EiNSTeiN-/roadrunner-filament-sensor/images/manual/001_parts.jpg

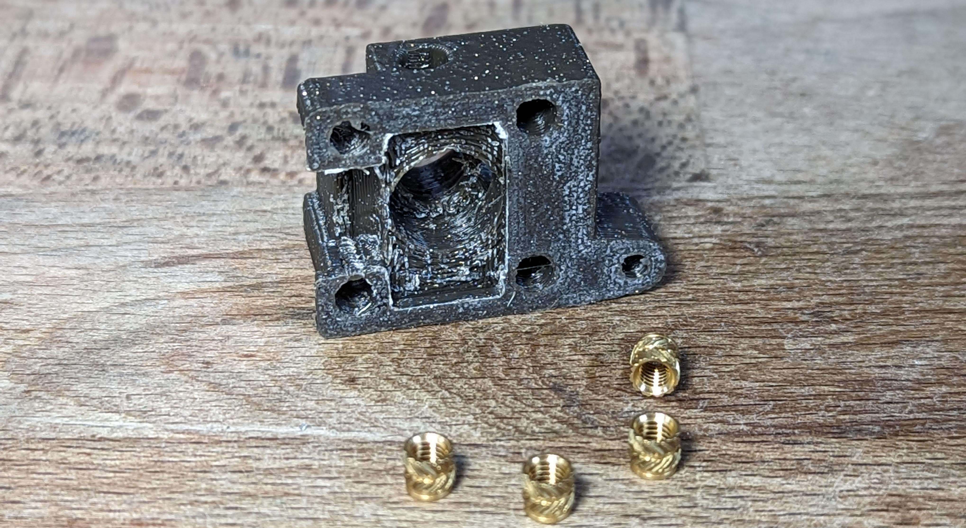
images/manual/001_parts.jpg
