EiNSTeiN-/roadrunner-filament-sensor/images/manual/002_parts.jpg

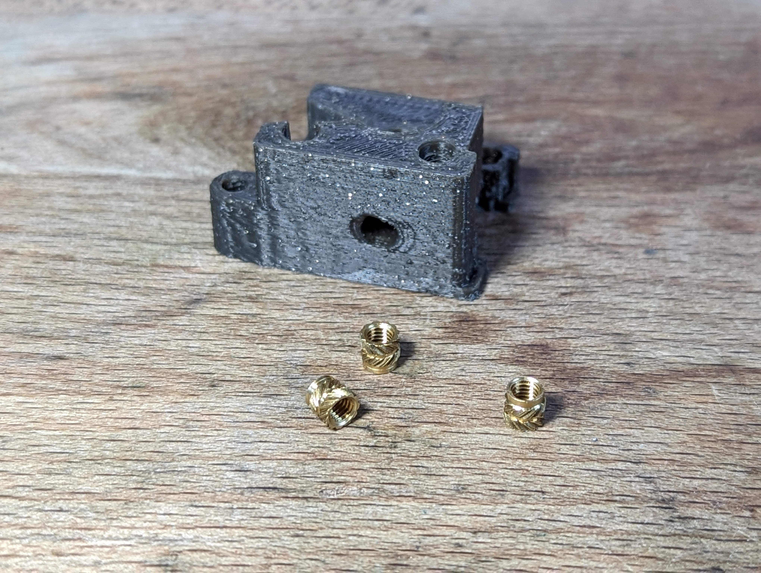
images/manual/002_parts.jpg
