EiNSTeiN-/roadrunner-filament-sensor/images/manual/012_assembled.jpg

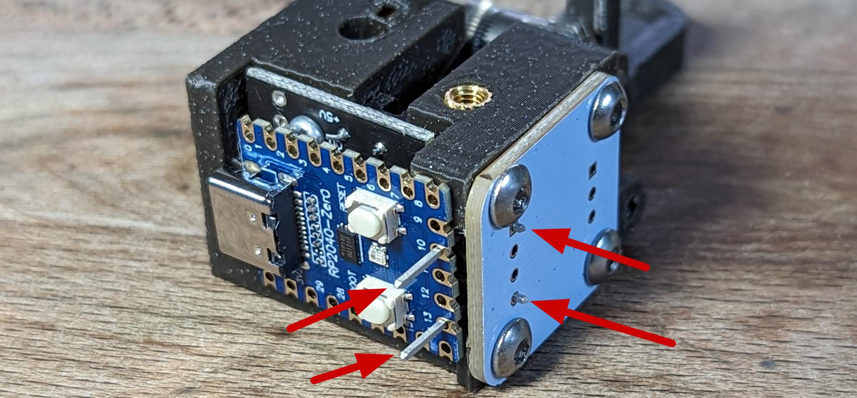
images/manual/012_assembled.jpg
