EiNSTeiN-/roadrunner-filament-sensor/images/manual/012_soldered_1.jpg

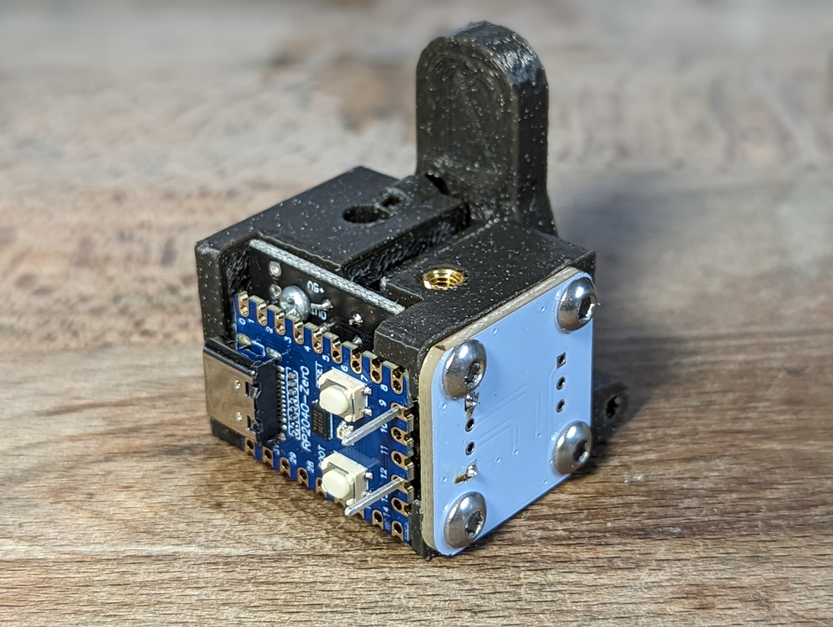
images/manual/012_soldered_1.jpg
