EiNSTeiN-/roadrunner-filament-sensor/images/manual/013_soldered_1.jpg

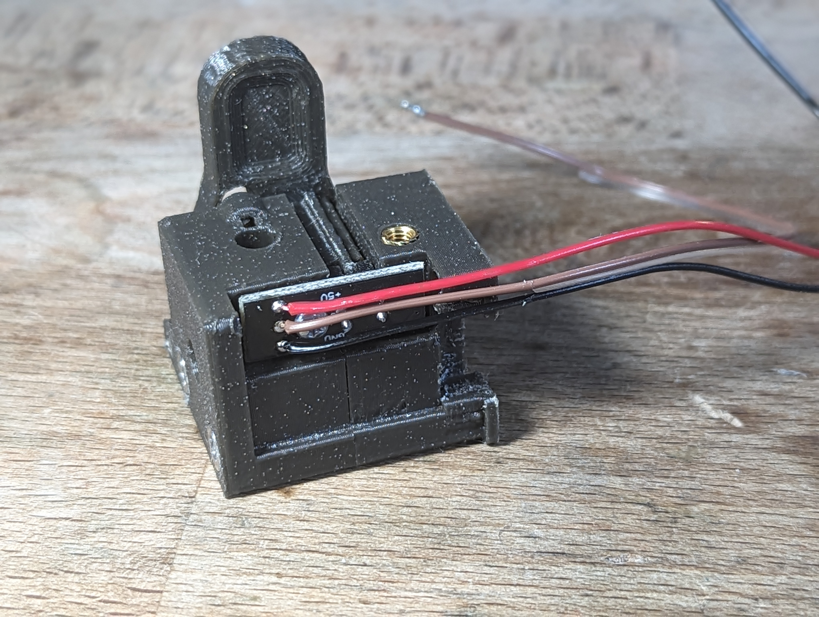
images/manual/013_soldered_1.jpg
