EiNSTeiN-/roadrunner-filament-sensor/images/manual/014_soldered_1.jpg

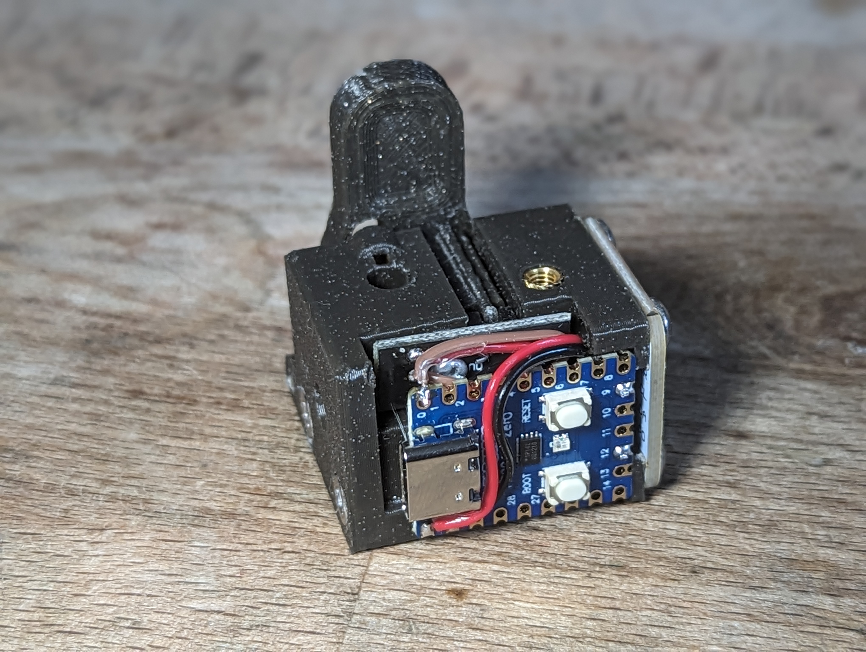
images/manual/014_soldered_1.jpg
