EiNSTeiN-/roadrunner-filament-sensor/images/manual/019_filament_inserted.png

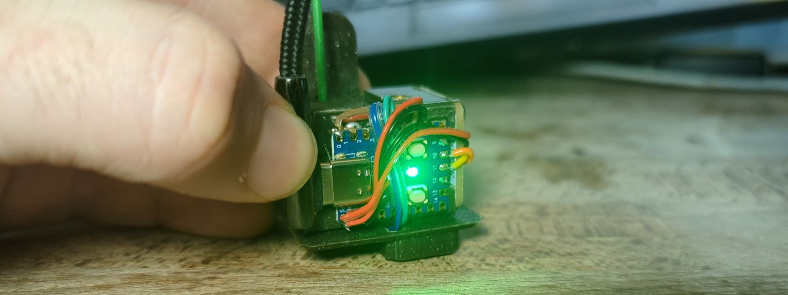
images/manual/019_filament_inserted.png
