EiNSTeiN-/roadrunner-filament-sensor/images/manual/019_no_filament.png

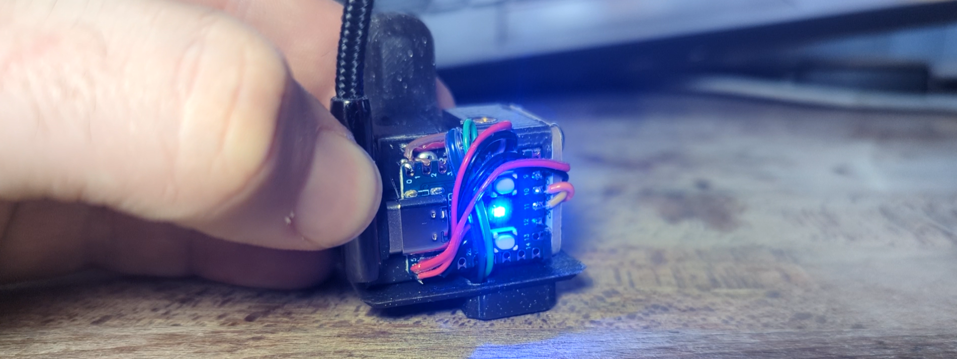
images/manual/019_no_filament.png
