EiNSTeiN-/roadrunner-filament-sensor/images/manual/020_assembled_2.jpg

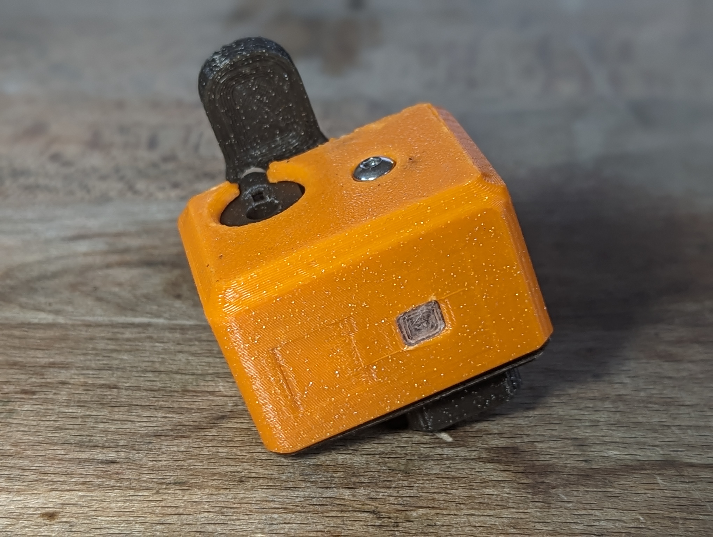
images/manual/020_assembled_2.jpg
