EiNSTeiN-/roadrunner-filament-sensor/klippy/extras/high_resolution_filament_sensor.py

# High Resolution Filament Sensor
#
# Copyright (C) 2023 Francois Chagnon <fc@francoischagnon.net>
#
# This file may be distributed under the terms of the GNU GPLv3 license.
import struct
import logging
import typing
import serialhdl
import serial
from . import bus, filament_switch_sensor, tmc_uart, high_resolution_filament_sensor_calibration as calibration

DEFAULT_I2C_TARGET_ADDR = 0x40
DEFAULT_I2C_SPEED = 100000

CHECK_RUNOUT_TIMEOUT = .100 # read sensor value at this interval

VIRTUAL_MOTION_PREFIX = 'virtual_motion_sensor'
VIRTUAL_SWITCH_PREFIX = 'virtual_switch_sensor'

class MagnetState:
    """" State of the rotary magnet encoder inside the sensor. """
    NOT_DETECTED = 1
    TOO_WEAK = 2
    TOO_STRONG = 3
    DETECTED = 4

    VALUES : dict[int, str] = {
        NOT_DETECTED: "not detected",
        TOO_WEAK: "too weak",
        TOO_STRONG: "too strong",
        DETECTED: "detected",
    }

    def __init__(self, value : int):
        self.value = value

    def __str__(self):
        return MagnetState.VALUES.get(self.value, "unknown")

    def __repr__(self):
        return "%s(value=%s)" % (self.__class__.__name__, repr(self.value))

class SensorRegister:
    """ Enum of registers that can be read from the sensor. """
    ALL = 0x10
    MAGNET_STATE = 0x21
    FILAMENT_PRESENCE = 0x22
    FULL_TURNS = 0x23
    ANGLE = 0x24

    def __init__(self, magnet_state, filament_presence, full_turns, angle):
        self.magnet_state = magnet_state
        self.filament_presence = filament_presence
        self.full_turns = full_turns
        self.angle = angle
        self.connected = not (magnet_state is None or
                                filament_presence is None or
                                full_turns is None or
                                angle is None)

class SensorEvent:
    """ A point-in-time reading from the sensor, which holds calculated
    values as well as additional printer state. """

    def __init__(self, eventtime : float, position : float, distance : float, epos : float):
        # eventtime at which this sensor reading was taken
        self.eventtime = eventtime

        # sensor position
        self.position = position

        # distance since previous reading from the sensor
        self.distance = distance

        # estimated extruder position at this eventtime
        self.epos = epos

    def __repr__(self):
        return "%s(eventtime=%s, position=%s, distance=%s, epos=%s)" % (
            self.__class__.__name__, self.eventtime, self.position, self.distance, self.epos)

class SensorUART(tmc_uart.MCU_TMC_uart_bitbang):
    """ Class for reading from the sensor via Klipper's native TMC uart driver. """

    def _remove_serial_bits(self, data : str) -> bytearray:
        """ Remove serial start and stop bits to a message in a bytearray. """
        mval = pos = 0
        for d in bytearray(data):
            mval |= d << pos
            pos += 8

        pos = 0
        res = bytearray()
        for i in range((len(data) * 8) // 10):
           shift = (i * 10) + 1
           res.append((mval >> shift) & 0xff)
        return res

    def _decode_read(self, reg : int, data : str) -> typing.Optional[bytearray]:
        """ Extract a uart read response message and returns the decoded message.
        Returns None when message cannot be verified. """
        decoded = self._remove_serial_bits(data)
        if len(decoded) < 5:
            return None
        if decoded[-1] != self._calc_crc8(decoded[:-1]):
            return None
        if decoded[0] != 0x05 and decoded[1] != 0xff:
            logging.warning("Received wrong message prefix: %s" % (decoded.hex(), ))
            return None
        if decoded[2] != reg:
            logging.warning("Received response for reg %02x (expected %02x)" % (decoded[2], reg))
            return None
        return decoded[3:-1]

    def reg_read(self, _instance_id, addr : int, reg : int, reg_length : int = 4) -> typing.Optional[bytearray]:
        """ Read a single register and returns a bytearray. """
        msg = self._encode_read(0xf5, addr, reg)
        read_length = (((4 + reg_length) * 10) + 7) // 8
        params = self.tmcuart_send_cmd.send([self.oid, msg, read_length])
        return self._decode_read(reg, params['read'])

class RegisterReaderGeneric:
    def __init__(self): pass
    def read(self) -> SensorRegister: raise NotImplementedError('must be implemented in subclass')

class RegisterReaderUART(RegisterReaderGeneric):
    def __init__(self, uart):
        self.uart = uart

    def read(self):
        magnet_state = self.uart_read_reg1(SensorRegister.MAGNET_STATE)
        filament_presence = self.uart_read_reg1(SensorRegister.FILAMENT_PRESENCE)
        full_turns = self.uart_read_reg4(SensorRegister.FULL_TURNS)
        angle = self.uart_read_reg4(SensorRegister.ANGLE)

        return SensorRegister(magnet_state, filament_presence, full_turns, angle)

    def uart_read_reg(self, reg, length, retries=5):
        for _ in range(retries):
            response = self.uart.reg_read(None, 0, reg, length)
            if response:
                break
        if response is None:
            logging.warning("Error reading from uart, no response received or CRC was invalid.")
        else:
            return response

    def uart_read_reg4(self, reg):
        if data := self.uart_read_reg(reg, 4):
            val, = struct.unpack('<l', data)
            return val

    def uart_read_reg1(self, reg):
        if data := self.uart_read_reg(reg, 1):
            val, = struct.unpack('<B', data)
            return val

class RegisterReaderI2C(RegisterReaderGeneric):
    def __init__(self, i2c):
        self.i2c = i2c
        self.printer = i2c.mcu.get_printer()

    def read(self):
        data = self.i2c_read_reg(SensorRegister.ALL, 10)
        if not data or len(data) != 10:
            if data:
                error = "expected 10 bytes but got %d: '%s'" % (len(data), data.hex(), )
            else:
                error = "communication error"
            logging.warning(f"Reading from sensor failed: {error}")
            return

        magnet_state, filament_presence, full_turns, angle = struct.unpack('<BBll', data)
        if magnet_state == 0xff:
            return

        return SensorRegister(magnet_state, filament_presence, full_turns, angle)

    def i2c_read_reg(self, reg, length):
        try:
            params = self.i2c.i2c_read([reg], length)
            return bytearray(params['response'])
        except (serialhdl.error, self.printer.command_error) as e:
            logging.warning(f"{self.name}: Unable to read: {e}")
            return

class RegisterReaderSerial(RegisterReaderGeneric):
    def __init__(self, serial : serial.Serial):
        self.serial = serial
        self.buffer = bytes()

    def read(self):
        try:
            if self.serial.write(bytearray([0xf5, SensorRegister.ALL])) != 2:
                logging.warning(f"Writing to serial failed")
                return

            while True:
                data = self.serial.read()
                if len(data) == 0:
                    break
                self.buffer += data

            marker = None
            for i in range(len(self.buffer)-1):
                if self.buffer[i] == 0x05 and self.buffer[i+1] == 0xff:
                    marker = i
                    break

            if marker is None:
                logging.warning(f"Failed to find register marker in buffer")
                self.buffer = bytes()
                return

            if len(self.buffer) < 13:
                logging.warning(f"Not enough bytes read for response")
                return

            if (r := self.buffer[marker+2]) != SensorRegister.ALL:
                logging.warning(f"Wrong register response ({r!r})")
                self.buffer = self.buffer[marker+1:]
                return

            data = self.buffer[marker+3:marker+13]
            self.buffer = self.buffer[marker+13:]
        except serial.SerialException:
            logging.error("Unable to communicate with sensor")
            return

        if not data or len(data) != 10:
            if data:
                error = "expected 10 bytes but got %d: '%s'" % (len(data), data.hex(), )
            else:
                error = "communication error"
            logging.warning(f"Reading from sensor failed: {error}")
            return

        magnet_state, filament_presence, full_turns, angle = struct.unpack('<BBll', data)
        if magnet_state == 0xff:
            return

        return SensorRegister(magnet_state, filament_presence, full_turns, angle)

class SensorRotationHelper:
    """ Helper class used to convert raw point-in-time readings from the sensor
    into an angular change since the previous reading. """

    def __init__(self, resolution : int, ignore_bits : int):
        self.resolution = resolution
        self.ignore_bits = ignore_bits

        # Maximum and minimum values that can be obtained from the sensor
        self.angle_max_value = (1 << resolution) - 1
        self.angle_min_value = (1 << ignore_bits)

        # Value used to mask lower bits of the raw angle value read from the printer.
        self.mask = (1 << ignore_bits) - 1

        # The cumulative angle value including all full turns,
        # kept in the sensor's original resolution.
        self._absolute_angular_position = 0

    @property
    def angular_resolution(self):
        """ Returns the resolution given the number of bits the sensor returns. """
        return (self.angle_min_value / float(self.angle_max_value) * 360.)

    def absolute_angular_position(self):
        """ Returns the cumulative number of degrees turned since the sensor was booted up. """
        return ((self._absolute_angular_position & ~self.mask) / float(self.angle_max_value) * 360.)

    def update_raw(self, turns, angle):
        """ Calculate the absolute position from the number of full turns and the relative angle. """
        self._absolute_angular_position = (turns * self.angle_max_value) + angle

class MotionDirection:
    """" Wrapper for the motion direction. """
    def __init__(self, distance : float):
        self.distance = distance

    def __str__(self):
        if not self.distance:
            return "idle"
        elif self.distance > 0:
            return "extruding"
        else:
            return "reversing"

    def __repr__(self):
        return f"{self.__class__.__name__}(distance={self.distance})"

class CommandedMove:
    """ Represents a movement that was commanded to the printer around a given eventtime.
    Also holds the sensor position and the estimated extruder position around this eventtime.

    When the printer is ordered to move its extruder motor by a certain amount, we know
    the commanded (final) position ahead of time before the motor actually starts moving.
    As we read data from the sensor, the measured distance between each sensor reading is
    accumulated until the move is completed.
    """

    def __init__(self, eventtime, pos, last_epos, epos):
        # eventtime when this move was started
        self.eventtime : float = eventtime

        # Sensor position when the move was started
        self.pos : float = pos

        # Last known toolhead position before the move was started.
        # This can be a reading up to `CHECK_RUNOUT_TIME` seconds in the past.
        self.last_epos : float = last_epos

        # The commanded position, i.e. the final position once this
        # move is done, possibly in the future.
        self.epos : float = epos

        # Expected distance travelled once this move is done.
        self.distance : float = epos - last_epos

        # False while the move is happening, True once the printer is stopped or another move starts.
        self.ended : bool = False

        # All `SensorEvent` objects that happened during this move
        self.sensor_events : list[SensorEvent] = []
        self.first_event : typing.Optional[SensorEvent] = None
        self.last_event : typing.Optional[SensorEvent] = None
        self.first_motion_event : typing.Optional[SensorEvent] = None
        self.last_motion_event : typing.Optional[SensorEvent] = None

    def __repr__(self):
        return f"CommandedMove(t={self.eventtime}, pos={self.pos}, last_epos={self.last_epos}, " + \
            f"epos={self.epos}, distance={self.distance}, expected_distance={self.expected_distance}, " + \
            f"measured_distance={self.measured_distance}, ended={self.ended}, " + \
            f"first={self.first_event.epos if self.first_event else None}, last={self.last_event.epos if self.last_event else None}" + \
            ")"

    def add_sensor_event(self, event, capture=False):
        if capture:
            self.sensor_events.insert(0, event)
        if self.first_event is None:
            self.first_event = event
        if event.distance != 0.:
            if self.first_motion_event is None:
                self.first_motion_event = event
            self.last_motion_event = event
        self.last_event = event

    @property
    def last_motion_eventtime(self) -> typing.Optional[float]:
        """ The most recent `eventtime` at which the sensor had a non-zero `distance` reading. """
        if self.last_motion_event:
            return self.last_motion_event.eventtime

    @property
    def first_motion_eventtime(self) -> typing.Optional[float]:
        """ The most recent `eventtime` at which the sensor had a non-zero `distance` reading. """
        if self.first_motion_event:
            return self.first_motion_event.eventtime

    def has_stopped_moving(self, duration=0.1) -> bool:
        if not (e := self.last_motion_eventtime):
            return False
        if self.last_event.distance != 0.:
            return False
        diff = self.last_event.eventtime - e
        return diff >= duration

    @property
    def duration(self) -> typing.Optional[float]:
        """ The actual duration of the move. """
        if e := self.last_motion_eventtime:
            return e - self.first_motion_eventtime

    @property
    def expected_distance(self) -> typing.Optional[float]:
        """ Returns distance that the extruder is expected to have travelled
        between the start of the move and the most recent sensor reading. """
        if self.last_event:
            return self.last_event.epos - self.last_epos

    @property
    def measured_distance(self) -> float:
        """ Returns the difference in sensor position between the first and last event. """
        if self.last_event:
            return self.last_event.position - self.first_event.position
        else:
            return 0.

    @property
    def speed(self) -> typing.Optional[float]:
        """ Returns the average speed during the move (measured distance divided by duration). """
        if d := self.duration:
            return self.measured_distance / d

    @property
    def extrusion_rate(self) -> float:
        """ Returns the extrusion rate, (measured distance over the expected distance). """
        if d := self.expected_distance:
            return self.measured_distance / d
        return 0.0

    @property
    def detected(self) -> bool:
        return self.measured_distance != 0.

    @property
    def direction(self) -> str:
        """ Returns which way the extruder is moving given a positive or negative distance value. """
        return MotionDirection(self.measured_distance)

class ExtruderMove:
    """ A copy of a move in the extruder queue. """

    def __init__(self, eventtime, start_pos, end_pos, accel_t, cruise_t, decel_t, start_v, cruise_v, accel, can_pressure_advance):
        self.eventtime = eventtime
        self.start_pos = start_pos
        self.end_pos = end_pos
        self.distance = abs(end_pos - start_pos)
        self.retract = end_pos - start_pos < 0.
        self.accel_t = accel_t
        self.cruise_t = cruise_t
        self.decel_t = decel_t
        self.move_t = accel_t + cruise_t + decel_t
        self.start_v = start_v
        self.cruise_v = cruise_v
        self.accel = accel
        self.can_pressure_advance = can_pressure_advance

    def __repr__(self):
        return f"ExtruderMove(eventtime={self.eventtime}, start_pos={self.start_pos}, end_pos={self.end_pos}, distance={self.distance}, " \
                f"accel_t={self.accel_t}, cruise_t={self.cruise_t}, decel_t={self.decel_t}, move_t={self.move_t}, " \
                f"start_v={self.start_v}, cruise_v={self.cruise_v}, accel={self.accel}, can_pressure_advance={self.can_pressure_advance!r})"

class ExtruderMoveQueue:
    """ Holds future extruder moves. """

    def __init__(self):
        self.queue : list[ExtruderMove] = []

    def add(self, eventtime, move):
        start_pos = move.start_pos[3]
        end_pos = move.end_pos[3]
        axis_r = move.axes_r[3]
        accel = move.accel * axis_r
        start_v = move.start_v * axis_r
        cruise_v = move.cruise_v * axis_r
        can_pressure_advance = bool(axis_r > 0. and (move.axes_d[0] or move.axes_d[1]))

        move = ExtruderMove(eventtime, start_pos, end_pos, move.accel_t, move.cruise_t, move.decel_t, start_v, cruise_v, accel, can_pressure_advance)
        self.queue.append(move)

    def advance_time(self, now):
        while len(self.queue) > 0:
            if self.queue[0].eventtime > now:
                break
            # event is in the past, remove it
            self.queue.pop(0)

    def find_move_at_time(self, eventtime):
        for move in self.queue:
            if eventtime > move.eventtime:
                return move

class TriggerOnChange:
    """ Calls a function when the value is changed from False to True, only once. """

    def __init__(self, value : typing.Optional[bool], fn):
        self._value : bool = value
        self._changed_time = None
        self._fn = fn

    def set(self, value : bool, eventtime: float):
        if value is not self._value:
            self._fn(self._value, value, eventtime)
            self._changed_time = eventtime
        self._value = value

    def __bool__(self):
        return bool(self._value)
    __nonzero__=__bool__

class VirtualButtonWrapper:
    def __init__(self, printer):
        self.printer = printer
        self.sensors = {}

        # wrapper requirements
        self.pin_list = []

    def register_sensor(self, sensor):
        self.sensors[sensor.name] = sensor

    def register_callback(self, sensor, cb):
        raise NotImplementedError('must be implemented in subclass')

    def setup_buttons(self, pin_params_list, callback):
        for pin_params in pin_params_list:
            sensor_name = pin_params['pin']
            if sensor_name not in self.sensors:
                raise self.printer.config_error(
                        "%s not a high_resolution_filament_sensor object")

            self.pin_list.append(pin_params)

            sensor = self.sensors[sensor_name]
            self.register_callback(sensor, callback)

class VirtualMotionWrapper(VirtualButtonWrapper):
    def register_callback(self, sensor, cb):
        sensor.register_motion_callback(cb)

class VirtualSwitchWrapper(VirtualButtonWrapper):
    def register_callback(self, sensor, cb):
        sensor.register_switch_callback(cb)

class RunoutHelper(filament_switch_sensor.RunoutHelper):
    def __init__(self, config, sensor):
        super().__init__(config)
        self._sensor = sensor

    def cmd_QUERY_FILAMENT_SENSOR(self, gcmd):
        return self._sensor.cmd_QUERY_FILAMENT_SENSOR(gcmd)

class HighResolutionFilamentSensor:
    """ A filament sensor from which we can get extremely accurate position readings. """

    def __init__(self, config):
        self.name = config.get_name().split()[-1]
        self.printer = config.get_printer()
        self.gcode = self.printer.lookup_object('gcode')
        self.buttons = self.printer.load_object(config, 'buttons')
        self.reactor = self.printer.get_reactor()
        self.runout_helper = RunoutHelper(config, self)
        self.main_mcu = None

        # Configuration
        self.serial_port = config.get("serial", None)
        self.regs : typing.Optional[RegisterReaderGeneric] = None
        if self.serial_port:
            self.baud = config.getint("baud", default=115200)
        elif uart := self._lookup_uart_bitbang(config):
            self.regs = RegisterReaderUART(uart)
        else:
            i2c = bus.MCU_I2C_from_config(config, DEFAULT_I2C_TARGET_ADDR, DEFAULT_I2C_SPEED)
            self.regs = RegisterReaderI2C(i2c)

        self.extruder_name = config.get('extruder')
        self.invert_direction = config.getboolean('invert_direction', False)
        self.rotation_distance = config.getfloat('rotation_distance', minval=0)
        self.underextrusion_max_rate = config.getfloat('underextrusion_max_rate', minval=0.0, maxval=1.0)
        self.underextrusion_period = config.getfloat('underextrusion_period', minval=0.0)
        self.move_evaluation_distance = config.getfloat('move_evaluation_distance', 3, minval=0.0)
        self.hysteresis_bits = config.getint('hysteresis_bits', 3, minval=0, maxval=12) # ignore lower 3 bits by default

        # Printer state
        self._commanded_moves : list[CommandedMove] = []
        self._extruder_move_queue = ExtruderMoveQueue()
        self._current_extruder_move = None
        self._capture_history : bool = False
        self.position = 0.0
        self._is_printing = False
        self._is_homing = False
        self._unhealthy = TriggerOnChange(False, self._unhealthy_changed)
        self._runout = TriggerOnChange(False, self._runout_changed)
        self._underextrusion_start_time = None
        self._underextruding = TriggerOnChange(False, self._underextruding_changed)
        self._status_evaluation_move = None

        # virtual pins for native klipper module compatibility
        self._motion_callbacks = []
        self._motion_callback_state = True
        self._switch_callbacks = []
        self.setup_buttons(VIRTUAL_MOTION_PREFIX, VirtualMotionWrapper)
        self.setup_buttons(VIRTUAL_SWITCH_PREFIX, VirtualSwitchWrapper)

        # Internal sensor state
        self._magnet_state = MagnetState(0xff)
        self._sensor_connected = TriggerOnChange(None, self._sensor_connected_changed)
        self._filament_present = TriggerOnChange(None, self._filament_present_changed)
        self._rotation_helper = SensorRotationHelper(12, self.hysteresis_bits) # 12 bits of precision, with configured hysteresis

        self._sensor_update_timer = self.reactor.register_timer(self._sensor_update_event)
        self.printer.register_event_handler('klippy:connect', self._handle_connect)
        self.printer.register_event_handler('klippy:ready', self._handle_ready)
        self.printer.register_event_handler('idle_timeout:printing', self._handle_printing)
        self.printer.register_event_handler('idle_timeout:ready', self._handle_not_printing)
        self.printer.register_event_handler('idle_timeout:idle', self._handle_not_printing)
        self.printer.register_event_handler('homing:homing_move_begin', self._handle_homing_begin)
        self.printer.register_event_handler('homing:homing_move_end', self._handle_homing_end)

        calibration.HighResolutionFilamentSensorCalibration(self)

    def cmd_QUERY_FILAMENT_SENSOR(self, gcmd):
        sensor_connected = "connected" if self._sensor_connected else "not connected"
        filament_present = "detected" if self._filament_present else "not detected"
        runout_detected = "detected" if self._runout else "not detected"
        underextruding_detected = "detected" if self._underextruding else "not detected"
        msg = f"Filament Sensor {self.name}:\n"
        msg += f"- sensor {sensor_connected}\n"
        msg += f"- filament {filament_present}\n"
        msg += f"- runout {runout_detected}\n"
        msg += f"- underextrusion {underextruding_detected}\n"
        msg += f"- resolution: {self._rotation_helper.resolution} bits (lower {self._rotation_helper.ignore_bits} bits are ignored)\n"
        msg += f"- smallest detectable angular change: {self.detectable_angle_change()} degree\n"
        msg += f"- smallest detectable movement: {self.detectable_distance_change()} mm\n"
        gcmd.respond_info(msg)

    def _handle_connect(self):
        """ Connect the serial port, if necessary. """
        try:
            if self.serial_port:
                ser = serial.Serial(self.serial_port, self.baud, timeout=0.05, write_timeout=0.05)
                self.regs = RegisterReaderSerial(ser)
        except serial.SerialException:
            raise self.printer.config_error(f"{self.name}: Could not connect to {self.serial_port}")

    def setup_buttons(self, prefix, klass):
        """ Register virtual buttons for use with filament_motion_sensor and filament_switch_sensor. """
        wrapper = self.buttons.mcu_buttons.get(prefix)
        if wrapper is None:
            self.buttons.mcu_buttons[prefix] = wrapper = klass(self.printer)

            ppins = self.printer.lookup_object('pins')
            ppins.register_chip(prefix, self)
        wrapper.register_sensor(self)

    def register_motion_callback(self, cb):
        self._motion_callbacks.append(cb)

    def register_switch_callback(self, cb):
        self._switch_callbacks.append(cb)

    def detectable_angle_change(self):
        return self._rotation_helper.angular_resolution

    def detectable_distance_change(self):
        return self._rotation_helper.angular_resolution / 360. * self.rotation_distance

    def _lookup_uart_bitbang(self, config) -> typing.Optional[SensorUART]:
        if not (rx_pin := config.get('uart_rx_pin', None)):
            return
        ppins = config.get_printer().lookup_object("pins")
        rx_pin_params = ppins.lookup_pin(rx_pin, can_pullup=True)
        tx_pin_params = ppins.lookup_pin(config.get('uart_tx_pin'), can_pullup=True)

        if rx_pin_params['chip'] is not tx_pin_params['chip']:
            raise ppins.error("%s uart rx and tx pins must be on the same mcu")

        return SensorUART(rx_pin_params, tx_pin_params, None)

    def _measured_underextrusion_rate(self, move):
        """ Return a measure of how much we are actually extruding
        compared to how much was expected based on the move queue.
        The rate is returned as a value from 0.0 to 1.0, with 0.0 meaning
        the measured rate matches the expected rate and 1.0 meaning
        no extrusion was detected at all but some was expected. """
        return min(1., max(-1., 1. - move.extrusion_rate)) if move else 0.0

    def _combine_moves(self, newer : CommandedMove, older : CommandedMove) -> CommandedMove:
        move = CommandedMove(older.eventtime, older.pos, older.last_epos, newer.epos)
        move.ended = newer.ended
        move.first_event = older.first_event or newer.first_event
        move.first_motion_event = older.first_motion_event or newer.first_motion_event
        move.last_motion_event = newer.last_motion_event or older.last_motion_event
        move.last_event = newer.last_event or older.last_event
        move.sensor_events = newer.sensor_events + older.sensor_events
        return move

    def _combine_all_commanded_moves(self, fn=None):
        move = None

        for _move in self._commanded_moves:
            if not move:
                move = _move
            else:
                move = self._combine_moves(move, _move)
            if fn and fn(move):
                break

        return move

    def _combine_moves_for_distance(self, distance):
        _stop_fn = lambda move: move.expected_distance is not None and move.expected_distance >= distance
        return self._combine_all_commanded_moves(_stop_fn)

    def get_combined_moves(self):
        return self._combine_all_commanded_moves()

    def get_status(self, eventtime):
        move = self._status_evaluation_move
        speed = move.speed if move and not move.ended else None

        return {
            "enabled": bool(self.runout_helper.sensor_enabled),
            "sensor_connected": bool(self._sensor_connected),
            "magnet_state": str(self._magnet_state),
            "filament_detected": bool(self._filament_present),
            # "debug": {
            #     "move": repr(move),
            # },
            "motion": {
                "detected": move.detected if move else False,
                "direction": str(move.direction) if move else "idle",
                "commanded_distance": move.distance if move and not move.ended else 0.0,
                "expected_distance": move.expected_distance if move else 0.0,
                "measured_distance": move.measured_distance if move else 0.0,
                "measured_speed": speed or 0.0,
                "measured_volumetric_flow": self.extruder.filament_area * speed if speed else 0.0,
            },
            "underextrusion_rate": self._measured_underextrusion_rate(move) if move and self._is_printing else 0.0,
            "underextrusion_detected": bool(self._underextruding),
            "runout": bool(self._runout),
            "position": self.position,
        }

    def _get_extruder_pos(self, eventtime):
        """ Find the estimated extruder position at the given eventtime. """
        if self.main_mcu:
            print_time = self.main_mcu.estimated_print_time(eventtime)
            return self.extruder.find_past_position(print_time)

    def _capture_extruder_move(self, move_time, move, ea_index):
        clock_time = self.main_mcu.print_time_to_clock(move_time)
        eventtime = self.main_mcu._clocksync.estimate_clock_systime(clock_time)
        self._extruder_move_queue.add(eventtime, move)
        return self.orig_extruder_process_move(move_time, move, ea_index)

    def _inspect_commanded_move(self, eventtime):
        """ Check if the commanded position of the extruder has changed and
        keep track of commanded moves. """

        if self.toolhead.get_extruder() is not self.extruder:
            return

        extruder_move = self._extruder_move_queue.find_move_at_time(eventtime)
        if extruder_move and self._current_extruder_move != extruder_move:
            move = CommandedMove(eventtime, self.position, extruder_move.start_pos, extruder_move.end_pos)
            self._commanded_moves.insert(0, move)
            self._current_extruder_move = extruder_move

        self._extruder_move_queue.advance_time(eventtime)

        while len(self._commanded_moves) > 100:
            self._commanded_moves.pop()

    def _sensor_connected_changed(self, old_value, new_value, eventtime):
        logging.info(f"{self.name}: 'sensor_connected' changed from {old_value} to {new_value}")

        if old_value is None:
            return
        if new_value:
            self._respond_info("Reconnected")
        else:
            self._respond_error("No longer connected or data cannot be read")

    def _filament_present_changed(self, old_value, new_value, eventtime):
        logging.info(f"{self.name}: 'filament_present' changed from {old_value} to {new_value}")

        for cb in self._switch_callbacks:
            cb(eventtime, new_value)

        if old_value is None:
            return
        if new_value:
            self._respond_info("Filament present")
        else:
            self._respond_error("Filament not present")

    def _update_state_from_sensor(self):
        """ Read data from sensor and sets the internal state to match. """

        eventtime = self.reactor.monotonic()
        self._inspect_commanded_move(eventtime)

        regs = self.regs.read()
        self._sensor_connected.set(bool(regs and regs.connected), eventtime)
        if not self._sensor_connected:
            return

        self._magnet_state = MagnetState(regs.magnet_state)
        self._filament_present.set(regs.filament_presence == 1, eventtime)

        self._rotation_helper.update_raw(regs.full_turns, regs.angle)

        inv = (-1 if self.invert_direction else 1)
        new_position = self.rotation_distance * (self._rotation_helper.absolute_angular_position() * inv) / 360.
        distance = new_position - self.position
        self.position = new_position

        if distance > 0.:
            # If we moved by any nonzero amount since previous measurement, toggle state and trigger callbacks
            self._motion_callback_state = not self._motion_callback_state
            for cb in self._motion_callbacks:
                cb(eventtime, self._motion_callback_state)

        if len(self._commanded_moves) > 0:
            move = self._commanded_moves[0]
            if not move.ended:
                event = SensorEvent(eventtime, self.position, distance, self._get_extruder_pos(eventtime))
                move.add_sensor_event(event, self._capture_history)

    def _handle_ready(self):
        """ Callback when printer becomes ready. """

        logging.info("[%s] ready" % (self.__class__.__name__, ))

        self.toolhead = self.printer.lookup_object('toolhead')
        self.extruder = self.printer.lookup_object(self.extruder_name)
        self.main_mcu = self.printer.lookup_object('mcu')

        self.orig_extruder_process_move = self.extruder.process_move
        self.extruder.process_move = self._capture_extruder_move

        self.reactor.update_timer(self._sensor_update_timer, self.reactor.NOW)

    def _handle_homing_begin(self, hmove):
        self._is_homing = True
        logging.info("[%s] homing begin (no sensor update)" % (self.__class__.__name__, ))

    def _handle_homing_end(self, hmove):
        self._is_homing = False
        logging.info("[%s] homing end (sensor update resumed)" % (self.__class__.__name__, ))

    def _handle_printing(self, print_time):
        """ Callback when printing starts. """

        logging.info("[%s] printing" % (self.__class__.__name__, ))
        eventtime = self.main_mcu.print_time_to_clock(print_time)
        self._runout.set(False, eventtime)
        self._underextrusion_start_time = None
        self._underextruding.set(False, eventtime)
        self._is_printing = True
        self.clear_move_queue()
        self._status_evaluation_move = None

    def _handle_not_printing(self, print_time):
        """ Callback when printing is finished. """

        logging.info("[%s] not printing" % (self.__class__.__name__, ))
        self._is_printing = False
        self.all_moves_ended()

    def _respond_error(self, msg):
        """ Print and error to the gcode console. """
        msg = f"{self.name}: {msg}"
        logging.warning(msg)
        lines = msg.strip().split('\n')
        if len(lines) > 1:
            self.gcode.respond_info("\n".join(lines), log=False)
        self.gcode.respond_raw('!! %s' % (lines[0].strip(),))

    def _respond_info(self, msg, log=False):
        self.gcode.respond_info(f"{self.name}: {msg}", log)

    def _exec_gcode(self, prefix, template):
        """ Execute the given gcode with error handling. """
        try:
            self.gcode.run_script(prefix + template.render() + "\nM400")
        except Exception:
            logging.exception("Script running error")
        self.runout_helper.min_event_systime = self.reactor.monotonic() + self.runout_helper.event_delay

    def _runout_event_handler(self, eventtime):
        """ Call the runout code and optionally pause the print. """
        pause_prefix = ""
        if self.runout_helper.runout_pause:
            # Pausing from inside an event requires that the pause portion
            # of pause_resume execute immediately.
            pause_resume = self.printer.lookup_object('pause_resume')
            pause_resume.send_pause_command()
            pause_prefix = "PAUSE\n"
            self.printer.get_reactor().pause(eventtime + self.runout_helper.pause_delay)
        self._exec_gcode(pause_prefix, self.runout_helper.runout_gcode)

    def _is_sensor_healthy(self):
        """ The sensor is 'unhealthy' when it stops responding, or when the magnet
        is too far from the magnetic rotary encoder."""
        return self._sensor_connected and \
            self._magnet_state.value == MagnetState.DETECTED

    def _sensor_unhealthy_reason(self) -> str:
        """ Returns a reason for the sensor being unhealthy for displaying in error messages. """
        if not self._sensor_connected:
            return "no data from sensor"
        if self._magnet_state.value != MagnetState.DETECTED:
            return "magnet %s" % (str(self._magnet_state), )
        return "unknown reason"

    def _is_runout_condition(self, eventtime):
        """ Checks whether there is a runout condition, either immediately when
        the filament is not detected, or after the configured period of time when
        underextruding. """

        if not self._filament_present:
            return True

        rate = self._measured_underextrusion_rate(self._status_evaluation_move)
        if rate > self.underextrusion_max_rate:
            if self._underextrusion_start_time is None:
                self._underextrusion_start_time = self.reactor.monotonic()
                # self._respond_error("Detected %.2f%% underextrusion starting at %.2f" %
                #                     (rate * 100, self._underextrusion_start_time))
                return False
            elif self._underextrusion_start_time + self.underextrusion_period < self.reactor.monotonic():
                self._underextruding.set(True, eventtime)
                return True
        elif self._underextrusion_start_time is not None:
            self._underextruding.set(False, eventtime)
            self._underextrusion_start_time = None

        return False

    def _unhealthy_changed(self, old_value, new_value, eventtime):
        logging.info(f"{self.name}: 'unhealthy' changed from {old_value} to {new_value}")
        if new_value is False:
            return

        if new_value is True:
            self._respond_error("Unhealthy (%s)" %
                                (self._sensor_unhealthy_reason(), ))
        else:
            self._respond_info("Became healthy again")

    def _runout_changed(self, old_value, new_value, eventtime):
        logging.info(f"{self.name}: 'runout' changed from {old_value} to {new_value}")

    def _underextruding_changed(self, old_value, new_value, eventtime):
        logging.info(f"{self.name}: 'underextruding' changed from {old_value} to {new_value}")

        if new_value:
            self._respond_error("Detected underextrusion for over %.2fs" %
                                (self.underextrusion_period, ))
        elif self._underextrusion_start_time:
            self._respond_info("Underextrusion cleared after %.2fs" %
                                    (self.reactor.monotonic() - self._underextrusion_start_time))

    def _check_print_issues(self, eventtime):
        """ Call runout code when print issues are detected. """

        if not self._is_printing:
           return

        if not self._is_sensor_healthy():
            if not self._unhealthy:
                self._unhealthy.set(True, eventtime)
                self._runout_event_handler(eventtime)
            return
        else:
            self._unhealthy.set(False, eventtime)

        if self._is_runout_condition(eventtime):
            if not self._runout:
                self._runout.set(True, eventtime)
                self._runout_event_handler(eventtime)
            return
        else:
            # runout restored
            self._runout.set(False, eventtime)

    def _sensor_update_event(self, eventtime):
        """ Periodic timer to fetch sensor data and update internal state. """

        if not self._is_homing:
            self._update_state_from_sensor()
            self._status_evaluation_move = self._combine_moves_for_distance(self.move_evaluation_distance)

            if eventtime >= self.runout_helper.min_event_systime and self.runout_helper.sensor_enabled:
                self._check_print_issues(eventtime)

        return eventtime + CHECK_RUNOUT_TIMEOUT

    def all_moves_ended(self):
        for move in self._commanded_moves:
            move.ended = True

    def clear_move_queue(self):
        self._commanded_moves = []

    def has_stopped_moving(self):
        if len(self._commanded_moves) > 0:
            return self._commanded_moves[0].has_stopped_moving()

    def capture_history(self, capture):
        self._capture_history = capture

def load_config_prefix(config):
    return HighResolutionFilamentSensor(config)
